rde-mato/0x2a002aElectronics/Firmware-PCB/HT16_keys_driver.c

#include <xc.h>
#include <sys/attribs.h>
#include "0x2a002a.h"


extern struct s_all all;

u8			HT16_read_keys_request = 0;
static u32			previous_key_scan = 0;
static u32			buttons_timers[32] = {0};
static const u32	long_pressed_limit = FREQUENCY / 256;
extern u8	I2C1_read_buf[];

void	int_init_HT16_press(void)
{
	HT16_INT_POLARITY = FALLING_EDGE;
	HT16_INT_FLAG_CLR;
	HT16_INT_PRIORITY = 2;
	HT16_INT_ENABLE = INT_ENABLED;
}

void	__ISR(_EXTERNAL_0_VECTOR, IPL2AUTO) HT16IntHandler(void) {
	HT16_read_keys_request = 1;
	TIMER5_VALUE = 0;
	TIMER5_ON;
	HT16_INT_ENABLE = INT_DISABLED;
	HT16_INT_FLAG_CLR;
}

void	__ISR(_TIMER_5_VECTOR, IPL3AUTO) Timer5Handler(void)
{
	TIMER5_INT_FLAG_CLR;
	HT16_read_keys_request = 1;
}

void	process_key_scan(void)
{
	static u8	previous_main_encoder = 0;
	u32			changed_buttons;
	u32			unchanged_pressed_buttons;
	u32			last_poll_interval;
	u32			newly_pressed_buttons;
	u32			newly_released_buttons;
	u8			main_encoder;
	u8			unchanged_pressed_count;
	u8			i;

	all.current_key_scan = (I2C1_read_buf[0] << 0 )
		| ((I2C1_read_buf[1] & 0b1111) << 8)
		| (I2C1_read_buf[2] << 12)
		| ((I2C1_read_buf[3] & 0b1111) << 20)
		| (I2C1_read_buf[4] << 24);
	main_encoder = I2C1_read_buf[5] & 0b1;
	last_poll_interval = TIMER1_VALUE;
	TIMER1_VALUE = 0;

	changed_buttons = all.current_key_scan ^ previous_key_scan;
	unchanged_pressed_buttons = all.current_key_scan & previous_key_scan;
	newly_pressed_buttons = all.current_key_scan & ~previous_key_scan;
	newly_released_buttons = ~all.current_key_scan & previous_key_scan;

	if (newly_pressed_buttons)
	{
		i = 0;
		unchanged_pressed_count = 0;
		while (i < 32)
		{
			if (newly_pressed_buttons & (1 << i))
				event_handler(E_KEY_PRESSED, i);
			if (unchanged_pressed_buttons & (1 << i))
				unchanged_pressed_count++;
			++i;
		}
		if (unchanged_pressed_count == 1)
			event_handler(E_KEY_COMBINATION_PRESSED, all.current_key_scan);
	}
	if (newly_released_buttons)
	{
		i = 0;
		while (i < 32)
		{
			if (newly_released_buttons & (1 << i))
				event_handler(E_KEY_RELEASED, i);
			++i;
		}
	}
	if (unchanged_pressed_buttons)
	{
		i = 0;
		while (i < 32)
		{
			if (buttons_timers[i] == LONG_PRESS_DONE)
				;
			else if ((unchanged_pressed_buttons & (1 << i)))
			{
				buttons_timers[i] += last_poll_interval;
				if(buttons_timers[i] > long_pressed_limit)
				{
					event_handler(E_KEY_LONG_PRESSED, i);
					buttons_timers[i] = LONG_PRESS_DONE;
				}
			}
			else
				buttons_timers[i] = 0;
			++i;
		}
	}
	else
	{
		while (i < 32)
			buttons_timers[i++] = 0;
	}
	previous_key_scan = all.current_key_scan;

	if (!previous_main_encoder && main_encoder)
	{
		event_handler(E_KEY_PRESSED, E_SOURCE_ENCODER_MAIN);
		led_toggle(0);
	}
	previous_main_encoder = main_encoder;

	if (!all.current_key_scan && !main_encoder)
	{
		TIMER5_OFF;
		HT16_INT_ENABLE = INT_ENABLED;
	}
}

void	key_scan(void)
{
	I2C1_read_callback(0xE0, 0x40, 6, &process_key_scan);
}

void	int_init_timer5(void)
{
	TIMER5_INT_FLAG_CLR;
	TIMER5_INT_PRIORITY = 3;
	TIMER5_INT_ENABLE = INT_ENABLED;
}

void	timer_1_init(void)
{
	TIMER1_STOP_AND_RESET;
	TIMER1_VALUE = 0;
	TIMER1_PRESCALE = TIMER_A_PRESCALE_256;
	TIMER1_ON;
}

void	timer_5_init(void)
{
	TIMER5_STOP_AND_RESET;
	TIMER5_VALUE = 0;
	TIMER5_PRESCALE = TIMER_B_PRESCALE_16;
	TIMER5_PERIOD = FREQUENCY / (16 * BUTTON_POLLS_PER_SECOND);
}
