rde-mato/0x2a002aElectronics/Firmware-PCB/LCD_templates.c

#include <xc.h>
#include <sys/attribs.h>
#include "0x2a002a.h"
#include <stdlib.h>
#include <stdio.h>

extern struct	s_all all;
static const	u8	notesnames[][3] = { "C", "C#", "D", "D#", "E", "F", "F#", "G", "G#", "A", "A#", "B", "C" };

void	request_template(u8 template)
{
	all.cur_template = template;
	SPI1Fbits.LCD_w = 1;
}

void	LCD_back_to_default(void)
{
	request_template(all.default_template);
}

u8	*negate_string(u8 *str, u8 *dest)
{
	u8	i;

	i = 0;
	while (dest[i])
		dest[i++] = 0;
	i = 0;
	while (str[i])
	{
		dest[i] = str[i] + 0x80;
		i++;
	}
	return (dest);
}

void	display_current_template(void)
{
	static u8	previous = TEMPLATE_DEFAULT;
	static u8	last_encoder = 0;
	u8			lines[LINES_COUNT][CHARS_PER_LINE + 1] = { 0 };
	u8			i = 0;
	u8			s1[CHARS_PER_LINE + 1] = "";
	u8			s2[CHARS_PER_LINE + 1] = "";

	if (all.cur_template == TEMPLATE_ENCODER && all.cur_template == previous)
	{
		snprintf(s1, CHARS_PER_LINE + 1, "%3d", (all.encoders_values[all.cur_encoder] + ENCODERS_STEP >= ENCODERS_MAX ? 100 :  100 * all.encoders_values[all.cur_encoder] / ENCODERS_MAX));
		LCD_print_char(3, 11, all.cur_encoder + '1' + 0x80);
		all.lcd_chars[3][11] = all.cur_encoder + '1' + 0x80;
		LCD_print_char(4, 7, s1[0]);
		all.lcd_chars[4][7] = s1[0];
		LCD_print_char(4, 8, s1[1]);
		all.lcd_chars[4][8] = s1[1];
		LCD_print_char(4, 9, s1[2]);
		all.lcd_chars[4][9] = s1[2];
		last_encoder = all.cur_encoder;
	}
	else
	{
		LCD_clear();
		switch (all.cur_template)
		{
			case TEMPLATE_DEFAULT:
				snprintf(lines[0], CHARS_PER_LINE + 1, "%10s%10s", negate_string("INSTRUMENT", s1), negate_string("PATTERN", s2));
				snprintf(lines[1], CHARS_PER_LINE + 1, "%10d%10d", all.cur_instrument + 1, all.cur_pattern + 1);
				snprintf(lines[3], CHARS_PER_LINE + 1, "%10s%10s", negate_string("NOTE", s1), negate_string("VELOCITY", s2));
				snprintf(lines[4], CHARS_PER_LINE + 1, "%10s%10d", notesnames[all.cur_note % 12], all.cur_velocity);
				snprintf(lines[6], CHARS_PER_LINE + 1, "%10s%10s", negate_string("BPM", s1), negate_string("OCTAVE", s2));
				snprintf(lines[7], CHARS_PER_LINE + 1, "%10.2f%10d", ((float)all.bpm_x100 / 100.0), all.cur_octave + 1);
				break;
			case TEMPLATE_BPM:
				snprintf(s1, CHARS_PER_LINE + 1, "%10s%20c", "BPM", 0);
				snprintf(lines[3], CHARS_PER_LINE + 1, "%10s", negate_string(s1, s2));
				snprintf(lines[4], CHARS_PER_LINE + 1, "%10.2f", ((float)all.bpm_x100 / 100.0));
				break;
			case TEMPLATE_ENCODER:
				snprintf(s1, CHARS_PER_LINE + 1, "%10s %d%20c", "ENCODER", all.cur_encoder + 1, 0);
				snprintf(lines[3], CHARS_PER_LINE + 1, "%10s", negate_string(s1, s2));
				snprintf(s1, CHARS_PER_LINE + 1, "%3d", (all.encoders_values[all.cur_encoder] + ENCODERS_STEP >= ENCODERS_MAX ? 100 :  100 * all.encoders_values[all.cur_encoder] / ENCODERS_MAX));
				break;
			case TEMPLATE_MAIN_MENU:
				snprintf(s1, CHARS_PER_LINE + 1, "%10s%20c", "MAIN MENU", 0);
				snprintf(lines[0], CHARS_PER_LINE + 1, "%10s", negate_string(s1, s2));
				i = 0;
				while (i < all.menu_items_count)
				{
					if (all.menu_items[i] == E_MENU_ITEMS_LOAD_FROM_SD)
						snprintf(lines[i + 2], CHARS_PER_LINE + 1, "%c %s", (i == all.menu_item_highlighted) ? '>': ' ', "Load from SD card");
					else if (all.menu_items[i] == E_MENU_ITEMS_LOAD_TO_SD)
						snprintf(lines[i + 2], CHARS_PER_LINE + 1, "%c %s", (i == all.menu_item_highlighted) ? '>': ' ', "Load to SD card");
					else if (all.menu_items[i] == E_MENU_ITEMS_COPY_PATTERN)
						snprintf(lines[i + 2], CHARS_PER_LINE + 1, "%c %s", (i == all.menu_item_highlighted) ? '>': ' ', "Copy pattern");
					else if (all.menu_items[i] == E_MENU_ITEMS_PASTE_PATTERN)
						snprintf(lines[i + 2], CHARS_PER_LINE + 1, "%c %s", (i == all.menu_item_highlighted) ? '>': ' ', "Paste pattern");
					else if (all.menu_items[i] == E_MENU_ITEMS_CLEAR_EEPROM)
						snprintf(lines[i + 2], CHARS_PER_LINE + 1, "%c %s", (i == all.menu_item_highlighted) ? '>': ' ', "Reset memory");
					else if (all.menu_items[i] == E_MENU_ITEMS_EXIT)
						snprintf(lines[i + 2], CHARS_PER_LINE + 1, "%c %s", (i == all.menu_item_highlighted) ? '>': ' ', "Exit");
					++i;
				}
				break;
			case TEMPLATE_NOTE:
				snprintf(s1, CHARS_PER_LINE + 1, "%10s%20c", "NOTE", 0);
				snprintf(lines[3], CHARS_PER_LINE + 1, "%10s", negate_string(s1, s2));
				snprintf(lines[4], CHARS_PER_LINE + 1, "%10s", notesnames[all.cur_note % 12]);
				break;
			case TEMPLATE_VELOCITY:
				snprintf(s1, CHARS_PER_LINE + 1, "%10s%20c", "VELOCITY", 0);
				snprintf(lines[3], CHARS_PER_LINE + 1, "%10s", negate_string(s1, s2));
				snprintf(lines[4], CHARS_PER_LINE + 1, "%10d", all.cur_velocity);
				break;
			case TEMPLATE_OCTAVE:
				snprintf(s1, CHARS_PER_LINE + 1, "%10s%20c", "OCTAVE", 0);
				snprintf(lines[3], CHARS_PER_LINE + 1, "%10s", negate_string(s1, s2));
				snprintf(lines[4], CHARS_PER_LINE + 1, "%10d", all.cur_octave + 1);
				break;
			case TEMPLATE_INSTRUMENT:
				snprintf(s1, CHARS_PER_LINE + 1, "%10s%20c", "INSTRUMENT", 0);
				snprintf(lines[3], CHARS_PER_LINE + 1, "%10s", negate_string(s1, s2));
				snprintf(lines[4], CHARS_PER_LINE + 1, "%10d", all.cur_instrument + 1);
				break ;
			case TEMPLATE_PATTERN:
				snprintf(s1, CHARS_PER_LINE + 1, "%10s%20c", "PATTERN", 0);
				snprintf(lines[3], CHARS_PER_LINE + 1, "%10s", negate_string(s1, s2));
				snprintf(lines[4], CHARS_PER_LINE + 1, "%10d", all.cur_pattern + 1);
				break ;
			case TEMPLATE_PATTERN_RECORDED:
				snprintf(s1, CHARS_PER_LINE + 1, "%10s%20c", "PATTERN RECORDED", 0);
				snprintf(lines[3], CHARS_PER_LINE + 1, "%10s", negate_string(s1, s2));
				break ;
			case TEMPLATE_LOADING_IN_PROGRESS:
				snprintf(s1, CHARS_PER_LINE + 1, "%10s %2d%%%20c", "LOADING :", all.loading_percentage, 0);
				snprintf(lines[3], CHARS_PER_LINE + 1, "%10s", negate_string(s1, s2));
				break ;
			case TEMPLATE_LOADING_SUCCESSFUL:
				snprintf(s1, CHARS_PER_LINE + 1, "%10s%20c", "LOADING SUCCESSFUL", 0);
				snprintf(lines[3], CHARS_PER_LINE + 1, "%10s", negate_string(s1, s2));
				break ;
			case TEMPLATE_CHIP_ERASED:
				snprintf(s1, CHARS_PER_LINE + 1, "%10s%20c", "MEMORY CLEARED", 0);
				snprintf(lines[3], CHARS_PER_LINE + 1, "%10s", negate_string(s1, s2));
				break ;
			case TEMPLATE_SD_ERROR:
				snprintf(s1, CHARS_PER_LINE + 1, "%10s%20c", "SD CARD ERROR", 0);
				snprintf(lines[3], CHARS_PER_LINE + 1, "%10s", negate_string(s1, s2));
				break ;

		}
		i = 0;
		while (i < LINES_COUNT)
		{
			LCD_putstr(i, 0, lines[i]);
			++i;
		}
		LCD_print_changed_chars();
	}
	if (all.cur_template != all.default_template && all.cur_template != TEMPLATE_LOADING_IN_PROGRESS)
		timer4_push(1000, &LCD_back_to_default);
	previous = all.cur_template;
}
