rde-mato/0x2a002aElectronics/Firmware-PCB/EEPROM.h

#ifndef EEPROM_H
#define EEPROM_H


#define EEPROM_BLOCK_SIZE	128

enum E_EEPROM_INSTRUCTIONS {
	E_EEPROM_READ = 0b00000011,
	E_EEPROM_WRITE = 0b00000010,
	E_EEPROM_WREN = 0b00000110,
	E_EEPROM_WRDI = 0b00000100,
	E_EEPROM_RDSR = 0b00000101,
	E_EEPROM_WRSR = 0b00000001,
	E_EEPROM_PE = 0b01000010,
	E_EEPROM_SE = 0b11011000,
	E_EEPROM_CE = 0b11000111,
	E_EEPROM_RDID = 0b10101011,
	E_EEPROM_DPD = 0b10111001,
	E_EEPROM_RDSR_WEL = 0b00000010,
	E_EEPROM_RDSR_WIP = 0b00000001
};

#endif
