rde-mato/0x2a002aElectronics/Firmware-POC/input_handler.c

#include <xc.h>
#include <sys/attribs.h>
#include "0x2a002a.h"


extern u32     current_key_scan;

u8  index = 0;
u32 cpt = 0;

extern u8 led;

void event_handler(u8 event_type, u8 event_source)
{
	switch (event_type)
	{
		case E_KEY_PRESSED:
			led_set(event_source);
			break;
		case E_KEY_RELEASED:
			led_toggle(event_source);
			break;
		case E_KEY_LONG_PRESSED:
			led_toggle(event_source);
			break;
		case E_ENCODER_TURNED_RIGHT:
			if (event_source == E_SOURCE_ENCODER_MAIN)
			{
				//led_toggle(index);
				//--index;
				//index &= 0x0F;
				//led_toggle(index);
                            cpt--;
			}
                        else if (event_source == 0)
                        {
                            led_toggle(led);
                            led = (led + 1) & 0xF;
                            led_toggle(led);
                        }
                        else if (event_source == 4)
                        {
                            led_toggle(led);
                            led = (led + 4) & 0xF;
                            led_toggle(led);
                        }
			break;
		case E_ENCODER_TURNED_LEFT:
			if (event_source == E_SOURCE_ENCODER_MAIN)
			{
//				led_toggle(index);
//				++index;
//				index &= 0x0F;
//				led_toggle(index);
                            cpt++;
			}
                        else if (event_source == 0)
                        {
                            led_toggle(led);
                            led = (led - 1) & 0xF;
                            led_toggle(led);
                        }
                        else if (event_source == 4)
                        {
                            led_toggle(led);
                            led = (led - 4) & 0xF;
                            led_toggle(led);
                        }
			break;


	}
}
